ridercz/GoProScad/Samples/STL/cold_shoe.stl

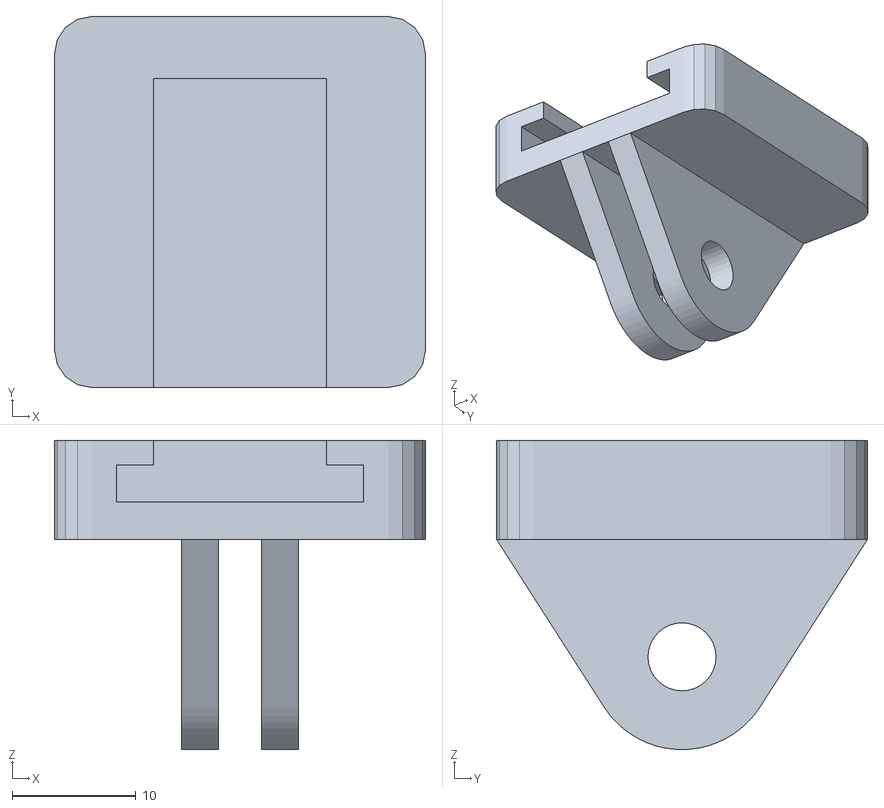
[picture p16: CAD file, 2024-05-07]
Samples/STL/cold_shoe.stl
30.0 x 30.0 x 25.0
