ridercz/GoProScad/Samples/STL/phone_holder_Nokia3.stl

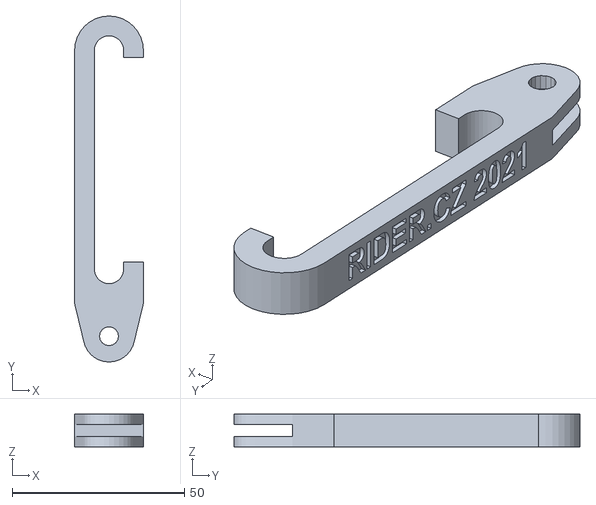
[picture p17: CAD file, 2024-05-07]
Samples/STL/phone_holder_Nokia3.stl
20.0 x 100.5 x 9.50
