ridercz/GoProScad/Samples/STL/phone_holder_A3.stl

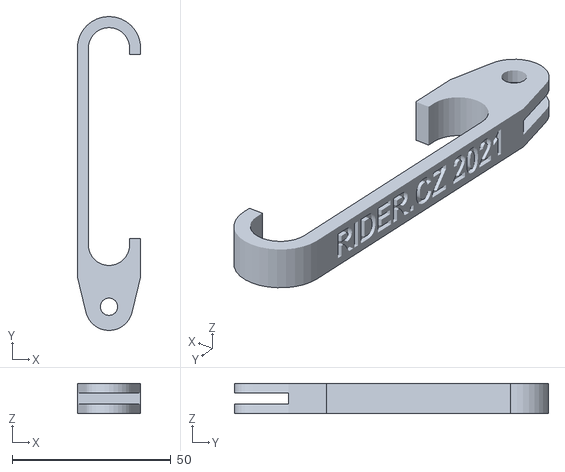
[picture p18: CAD file, 2024-05-07]
Samples/STL/phone_holder_A3.stl
20.0 x 99.0 x 9.50
