ridercz/GoProScad/Samples/STL/M6_mount.stl

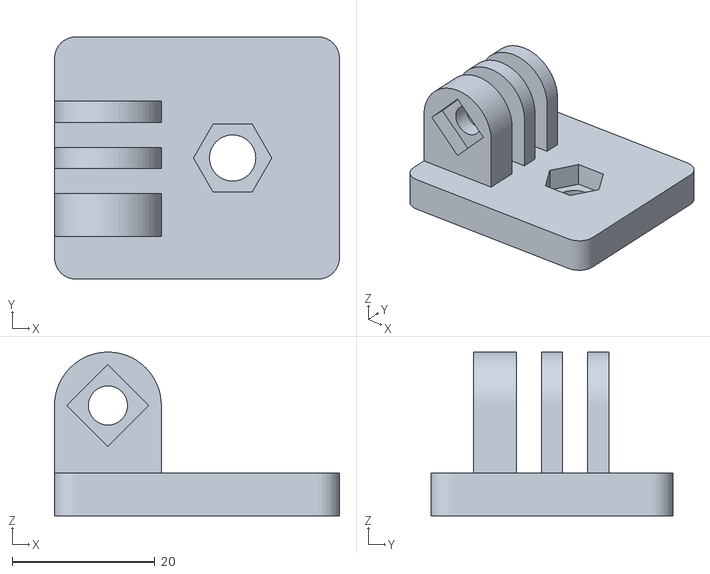
[picture p19: CAD file, 2021-12-30]
Samples/STL/M6_mount.stl
40.0 x 34.0 x 23.0
